ssbingo/asksin-analyzer-rpi/docs/handbuch/img/layout-1.png

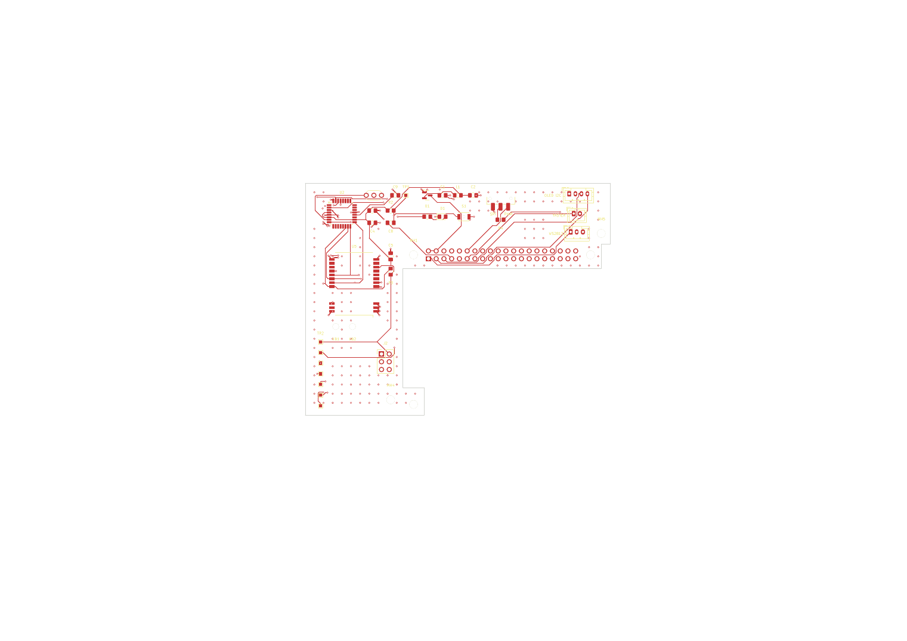
docs/handbuch/img/layout-1.png
