ssbingo/asksin-analyzer-rpi/docs/handbuch/img/oled-seiten.png

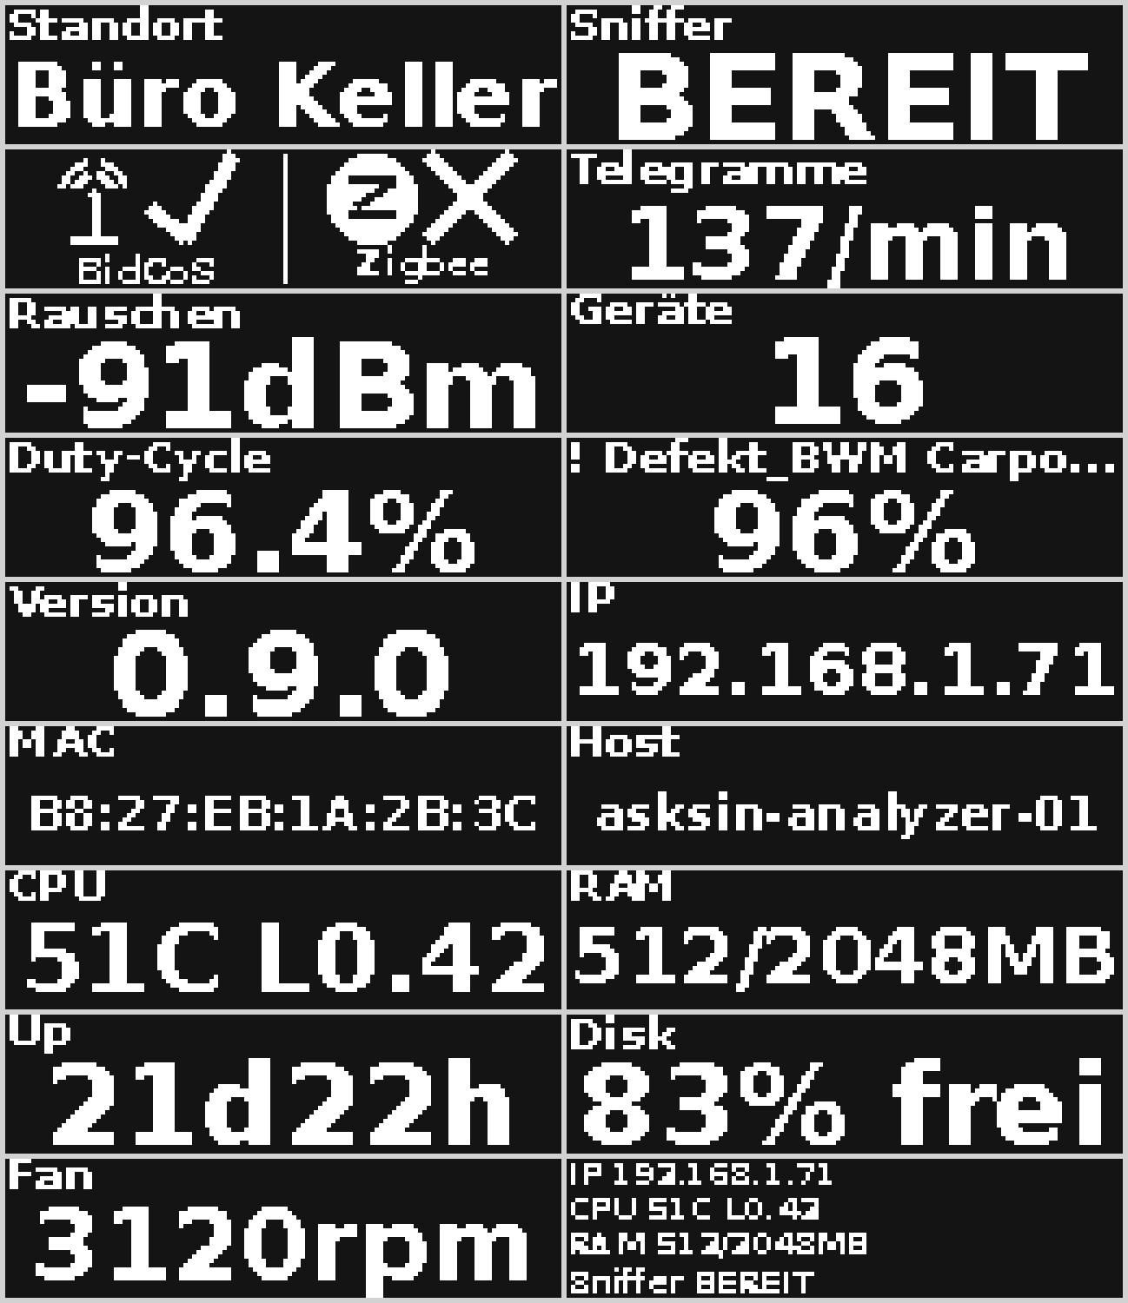
docs/handbuch/img/oled-seiten.png
