ssbingo/asksin-analyzer-rpi/docs/handbuch/img/ui-info.png

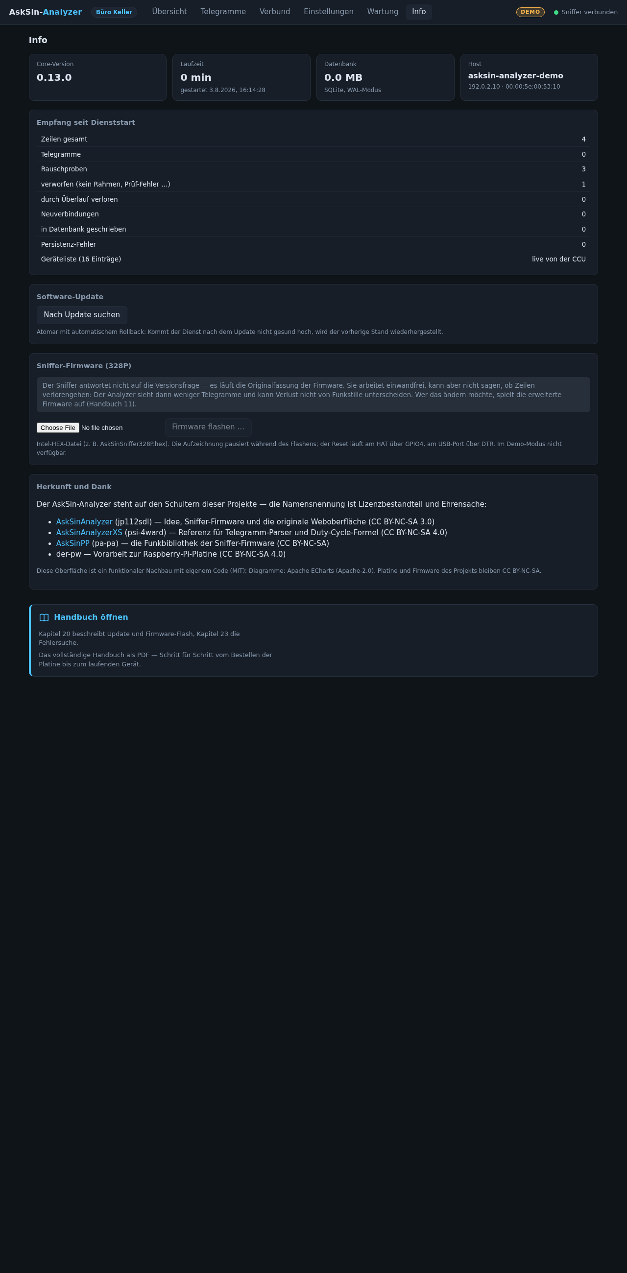
docs/handbuch/img/ui-info.png
