ssbingo/asksin-analyzer-rpi/docs/handbuch/img/ui-telegramme.png

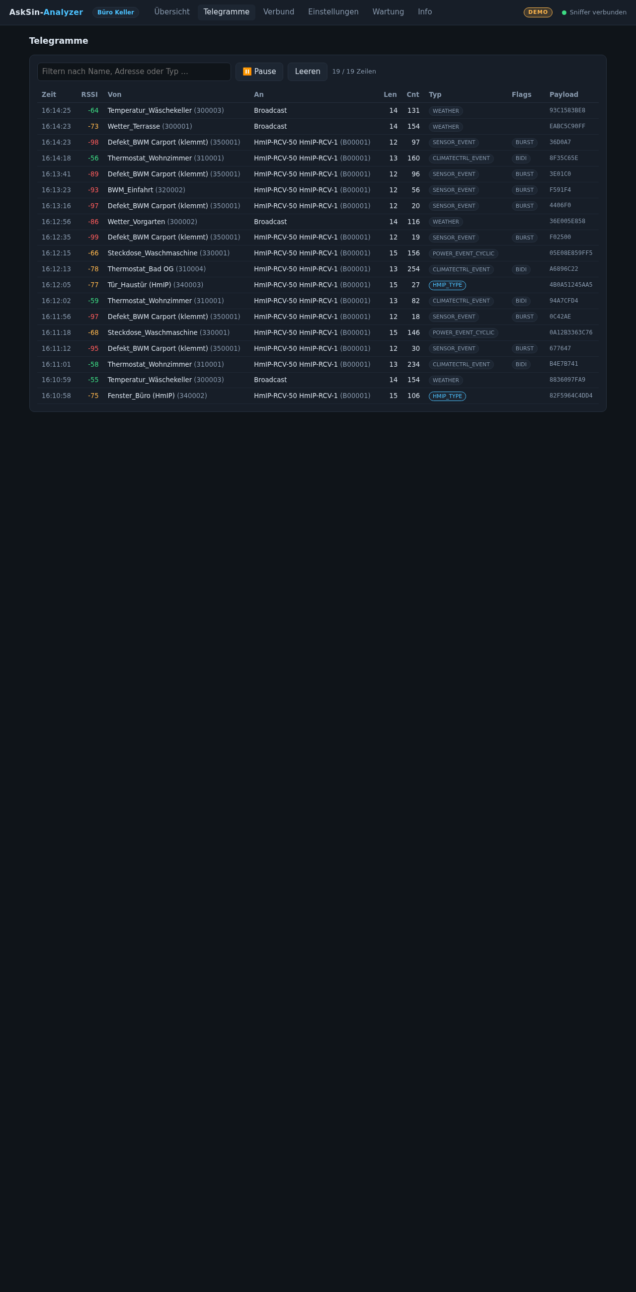
docs/handbuch/img/ui-telegramme.png
