ssbingo/asksin-analyzer-rpi/docs/handbuch/img/ui-uebersicht.png

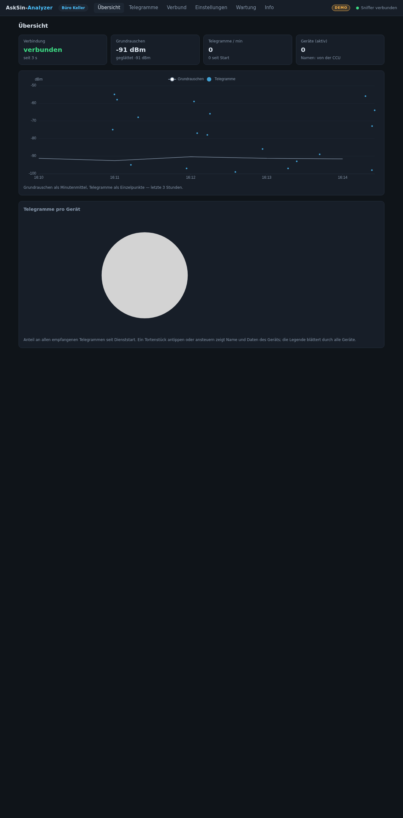
docs/handbuch/img/ui-uebersicht.png
