ssbingo/asksin-analyzer-rpi/docs/handbuch/img/ui-verbund.png

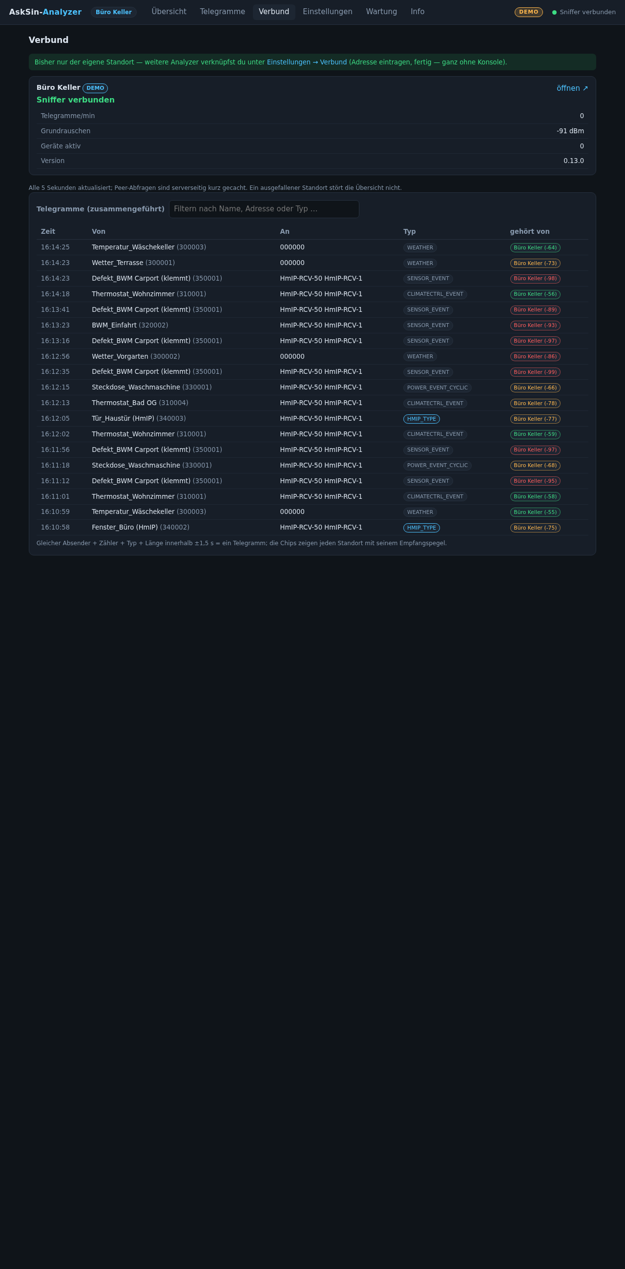
docs/handbuch/img/ui-verbund.png
