ssbingo/asksin-analyzer-rpi/docs/handbuch/img/ui-wartung.png

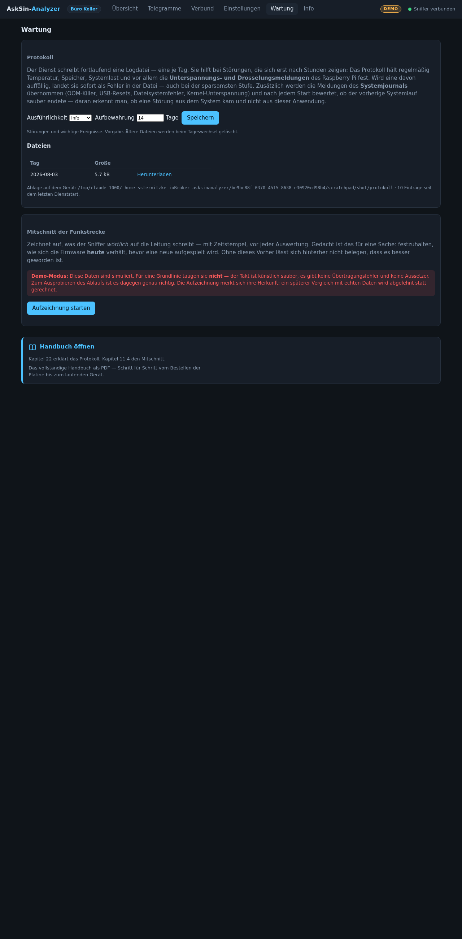
docs/handbuch/img/ui-wartung.png
